hildebkg/FahrradTech/img/bike_computer_PCB_3D_view_bottom.png

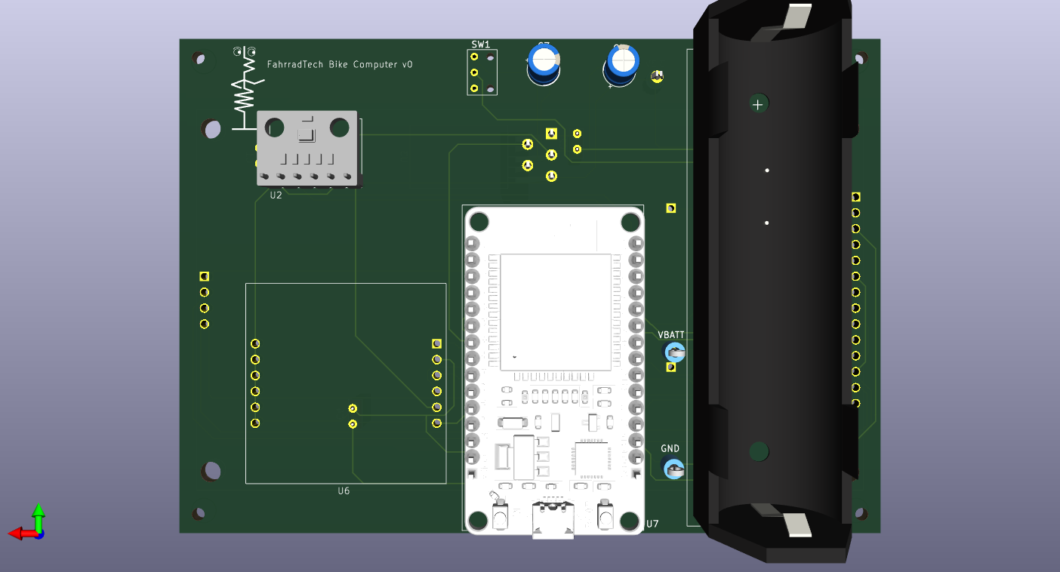
img/bike_computer_PCB_3D_view_bottom.png
