hildebkg/FahrradTech/img/bike_computer_PCB_3D_view_top.png

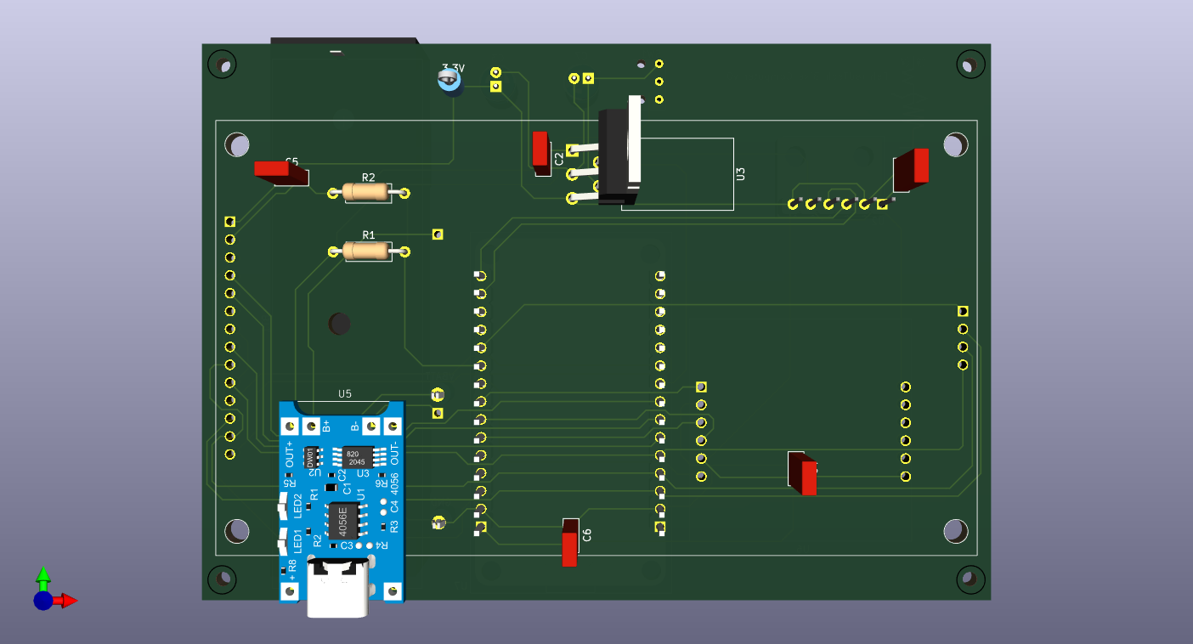
img/bike_computer_PCB_3D_view_top.png
