hildebkg/FahrradTech/img/BME_280_demo_sc.png

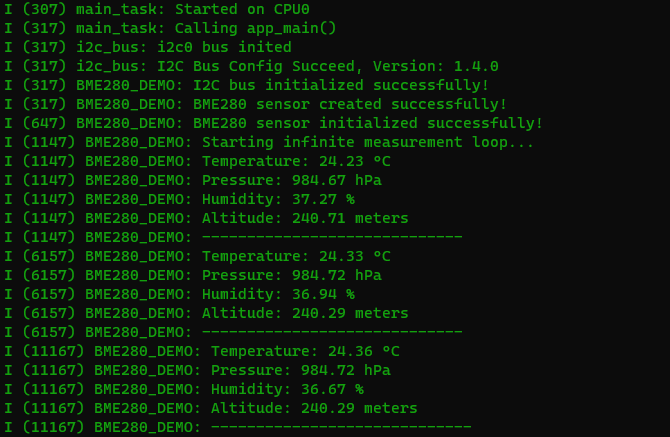
img/BME_280_demo_sc.png
