hildebkg/FahrradTech/img/rear_lights_unit_control_box_PCB_3D_view_top.png

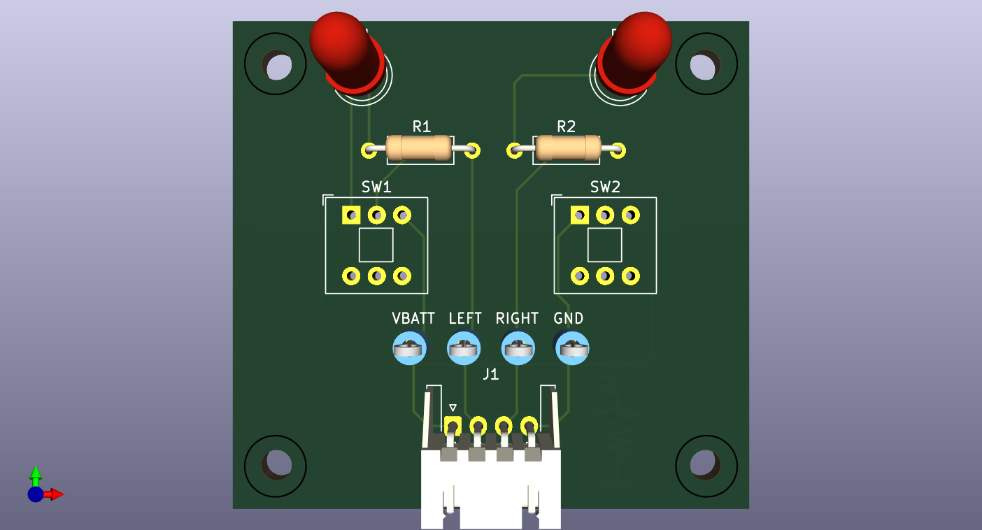
img/rear_lights_unit_control_box_PCB_3D_view_top.png
