hildebkg/FahrradTech/img/rear_lights_unit_PCB_3D_view_top.png

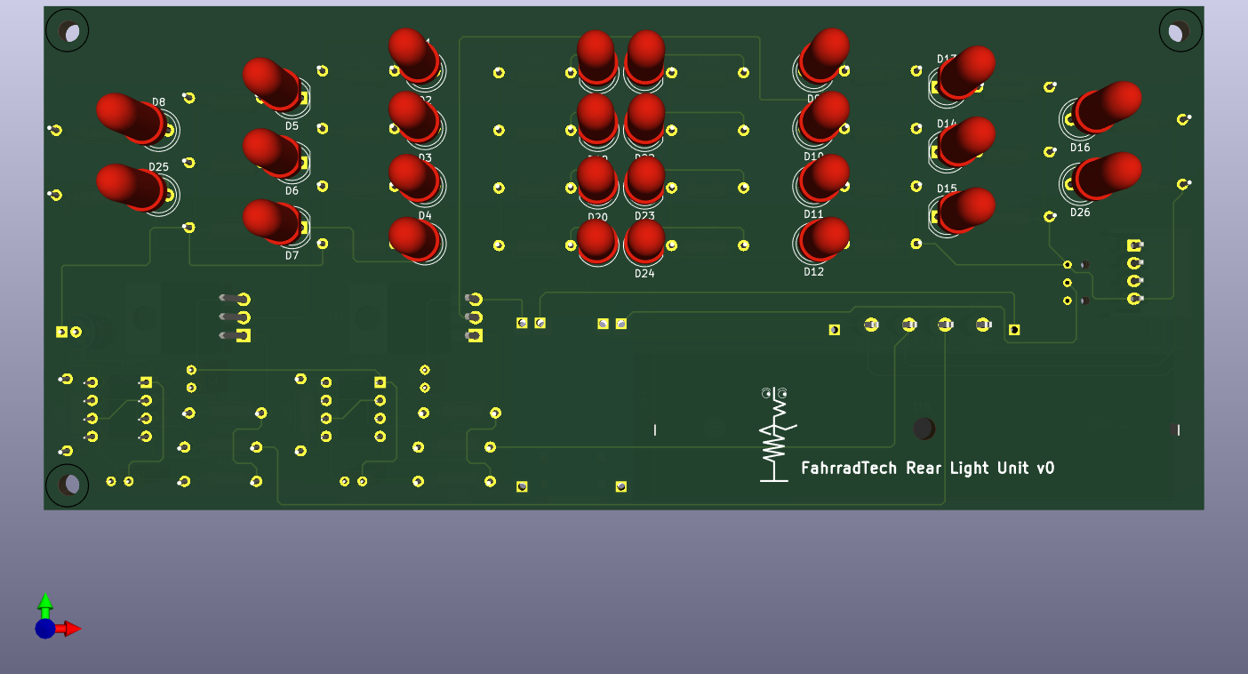
img/rear_lights_unit_PCB_3D_view_top.png
