hildebkg/FahrradTech/sim/light_control.png

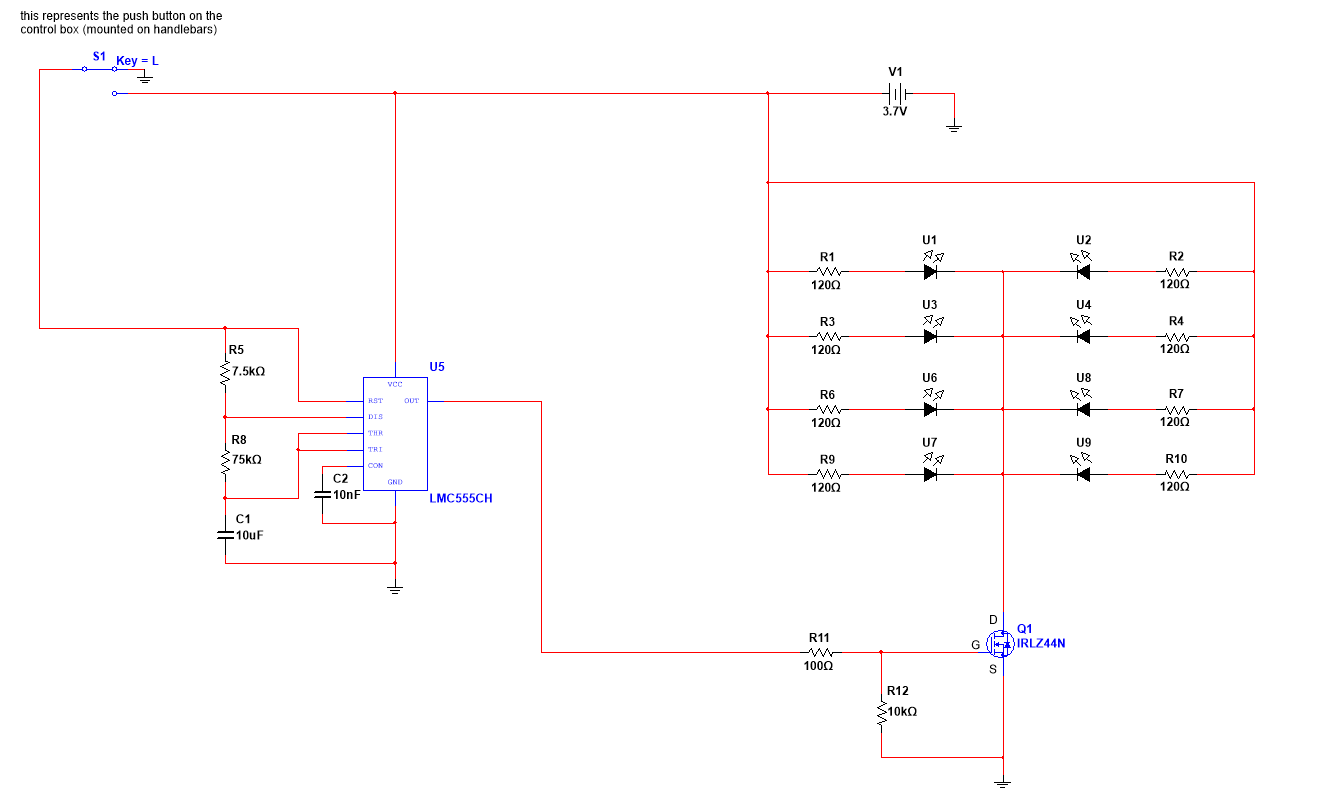
sim/light_control.png
